W3AXL/PanaTap/circuit.asc

C1: cap; 1n
C2: cap; 0.1µ
C3: cap; 1n
C4: cap; 0.1µ
C5: cap; 1n
C6: cap; 59p
C7: cap; 69p
C8: cap; 59p
J1: njf; J310_XN
L1: ind; 84n
L2: ind; 185n
L3: ind; 185n
L4: ind; 84n
Q1: npn; BFS17
R1: res; 220
R2: res; 100k
R3: res; 1k
R4: res; 39k
R5: res; 100
R6: res; 1k
V1: voltage; ""; AC 0.316
V2: voltage; 12
Named nets: 0
.MODEL J310_XN NJF(Beta=3.384m Betatce=-500m Rd=1 Rs=1 Lambda=17m Vto=-3.409 Vtotc=-2.5m Is=193.9f 
+ Isr=1.881p N=1 Nr=2 Xti=3 Alpha=7.533u Vk=74.1 Cgd=6.2p M=464.7m 
+ Pb=1 Fc=500m Cgs=6.2p Kf=4.634e-002f Af=1)
.MODEL BFS17  NPN IS =4.9E-16 NF =.993 BF =93 VAF=90 IKF=.055 
+             ISE=1E-14 NE =1.800 BR =25 VAR=6 NR =1.005 IKR=.01 
+             ISC=4.5E-15 NC =1.2 RB =7 RBM=.5 IRB=5E-4 RE =.5 
+             RC =2.0 TF =5E-11 XTF=100 ITF=2.3 TR =2.4E-8 
+             CJE=1.18E-12 CJC=1.54E-12 VJC=.559 MJC=.25 VJE=1.12 
+             MJE=.4
.ac oct 100 1Meg 200Meg
